Barabrad/itp388_Sp24Proj/src/secrets_def.h

// Default WiFi Credentials
#define SECRET_SSID "USC Guest Wireless"
#define SECRET_PASS ""
// Default Blynk Credentials
#define BLYNK_TEMPLATE_ID "[REDACTED]"
#define BLYNK_TEMPLATE_NAME "388 Project"
#define BLYNK_AUTH_TOKEN "[REDACTED]"
